FPGA-Computer/Swiftlet/Sonar Samples/corridor2.jpg

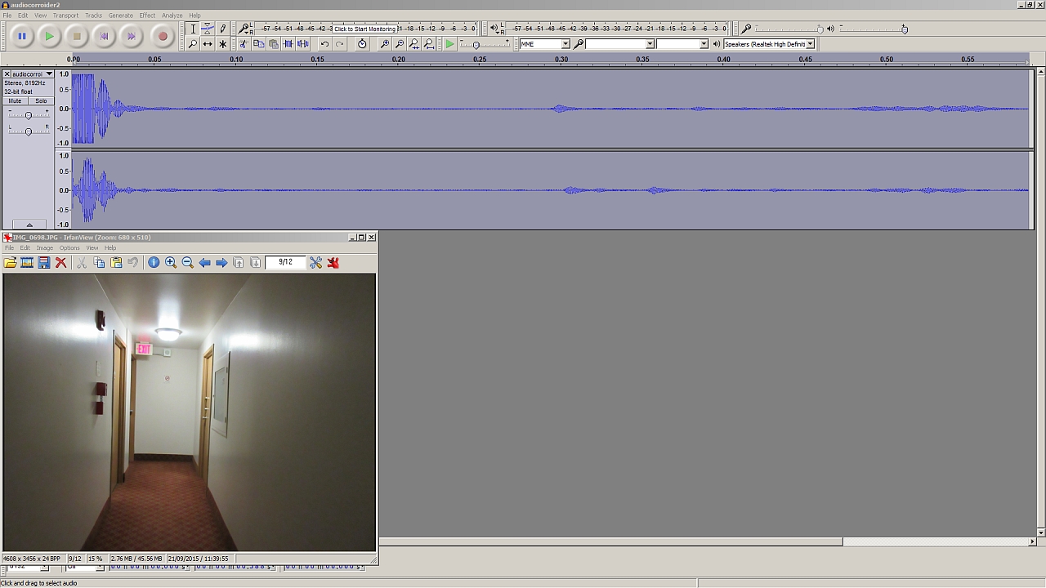
Sonar Samples/corridor2.jpg
