FPGA-Computer/Swiftlet/Ver 0.0 Rel 0/Eagle PCB/''Swiftlet'' Sonar for the Visually Impaired Ver 0.0 Rel 0 - Bare PCB Top.png

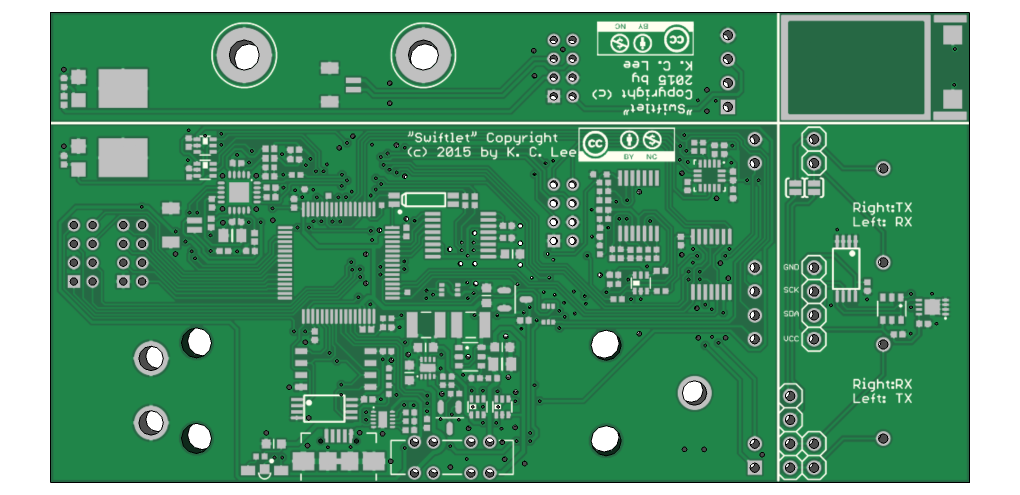
Ver 0.0 Rel 0/Eagle PCB/''Swiftlet'' Sonar for the Visually Impaired Ver 0.0 Rel 0 - Bare PCB Top.png
