FPGA-Computer/Swiftlet/Ver 0.0 Rel 0/LTSpice/receiver-4 .asc

C1: cap; 1nF
C2: cap; 1nF
C3: cap; 1nF
R1: res; 10K
R2: res; 220K
R3: res; 1.5K
R4: res; 1K
R5: res; 22K
U1: opamp2; lm2904
U2: opamp2; lm2904
V1: voltage; 3.3V
V2: voltage; SINE(0 15mV 40000); AC 0.1V
V3: voltage; 1.65V
Named nets: 0, Vout, vin
.include "lm2904.lib"
.tran 5ms uic
;ac dec 100 10000 100000
